skywoman/ChickenEnclosure/CAD/U Bolt.FCStd

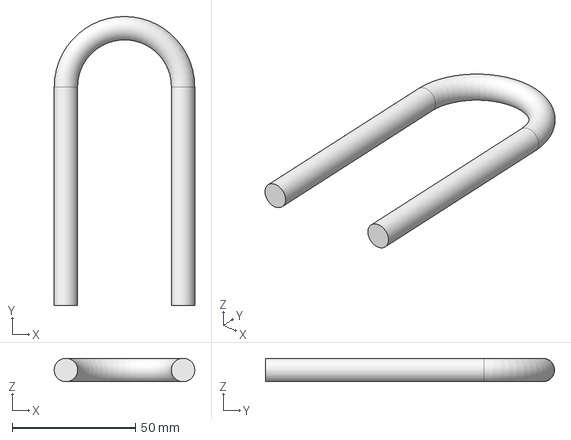
[picture p16: CAD file, 2022-02-22]
CAD/U Bolt.FCStd
57.1 x 117.5 x 9.52 mm
