skywoman/ChickenEnclosure/CAD/Hoop Connection - U Bolts/Side Bar Welded.pdf

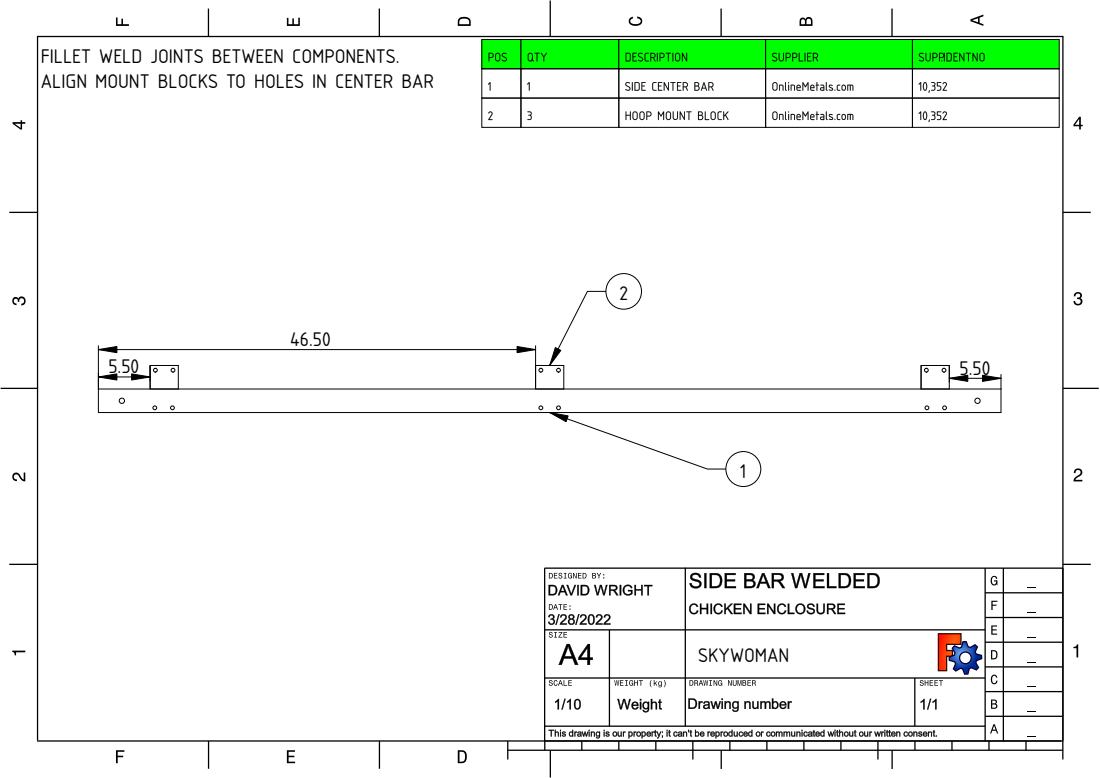
[picture p23: page 1]
SKYWOMAN

FILLET WELD JOINTS BETWEEN COMPONENTS. ALIGN MOUNT BLOCKS TO HOLES IN CENTER BAR
