skywoman/ChickenEnclosure/CAD/Hoop Connection - U Bolts/Side Front Bar.pdf

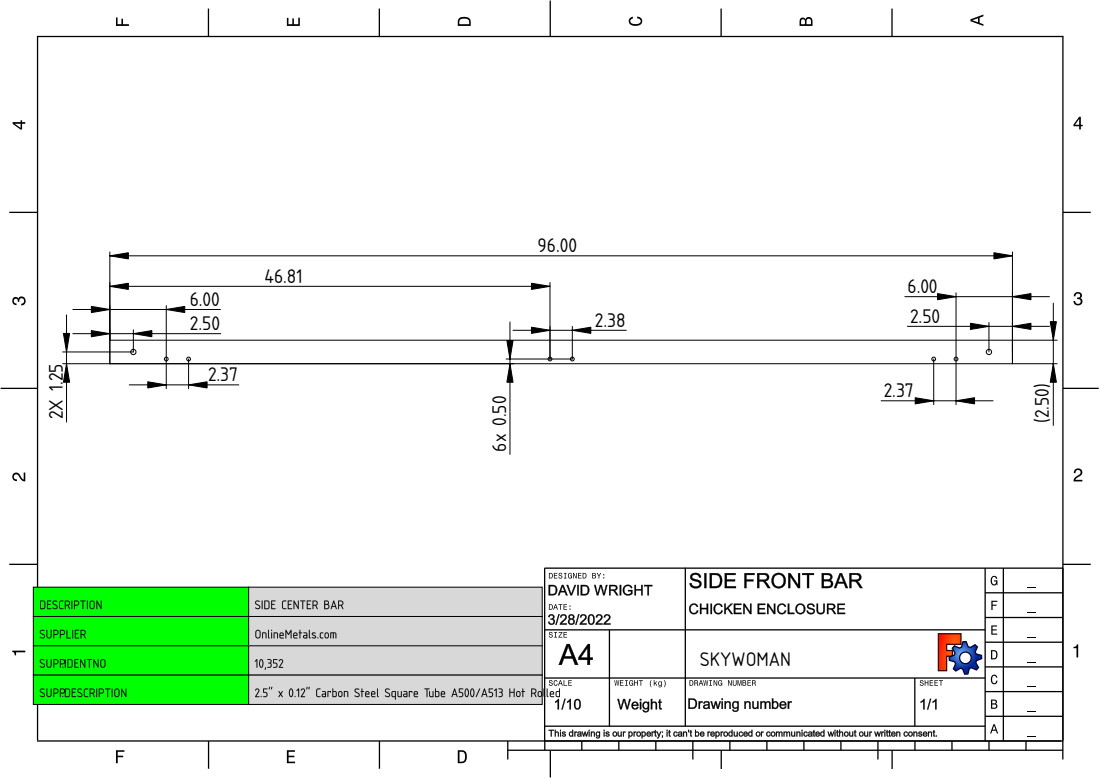
[picture p30: page 1]
