skywoman/ChickenEnclosure/CAD/Hoop Connection - U Bolts/Side Rail Joint Plate.pdf

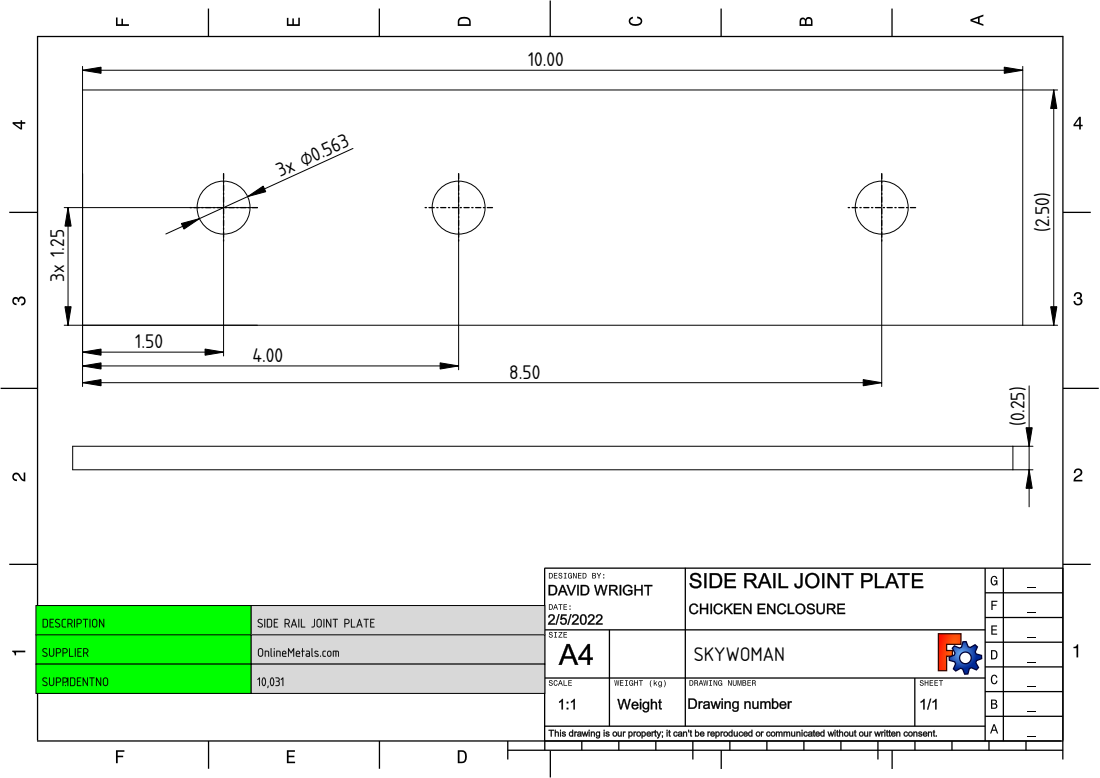
[picture p31: page 1]
