skywoman/ChickenEnclosure/CAD/Hoop Connection - U Bolts/Skid Angled Foot.pdf

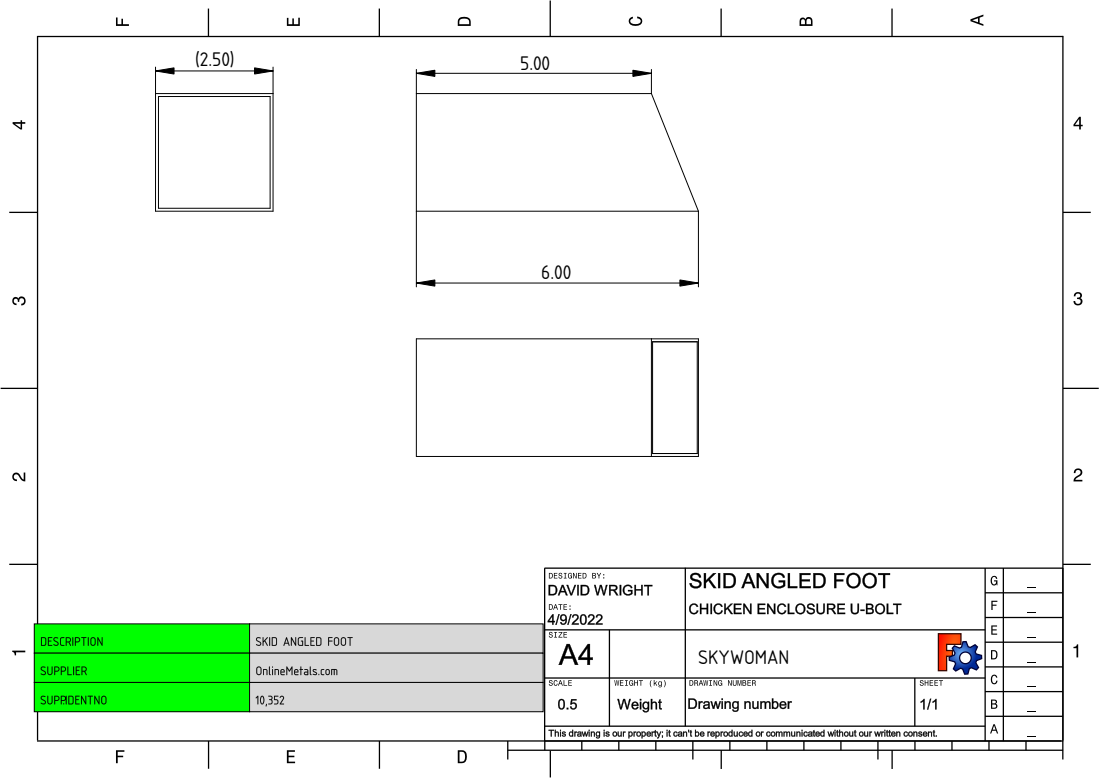
[picture p32: page 1]
SKYWOMAN
