skywoman/ChickenEnclosure/CAD/Hoop Connection - U Bolts/U Bolt.pdf

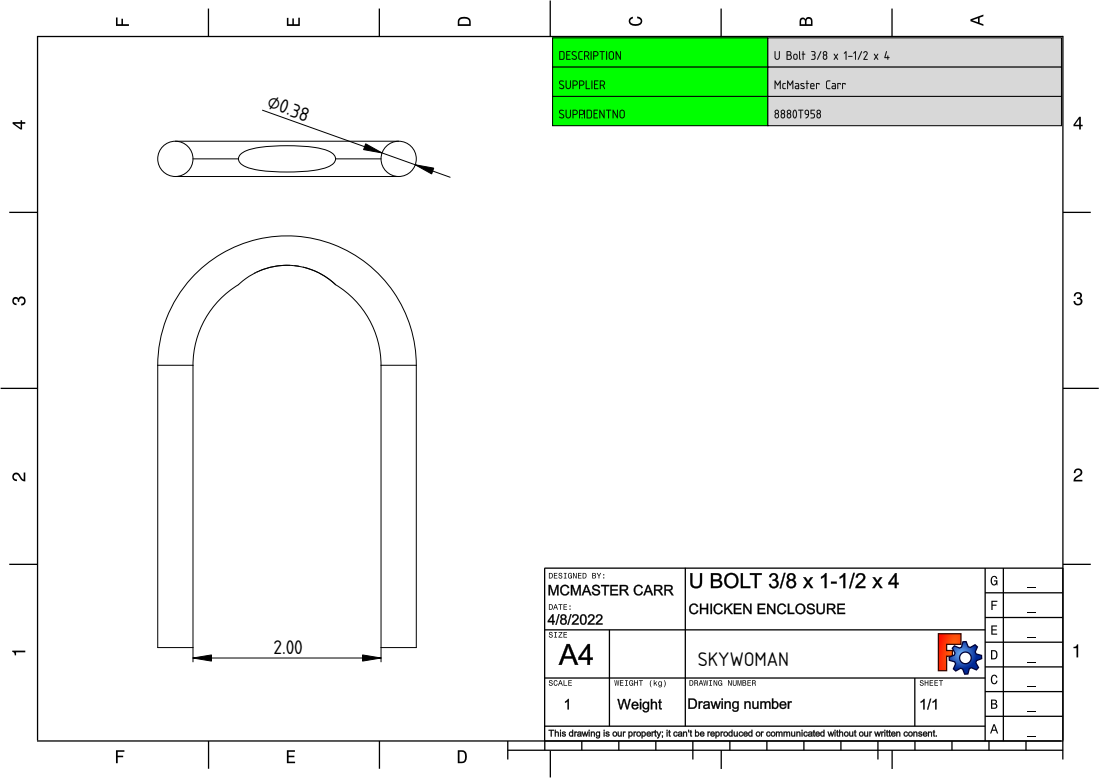
[picture p33: page 1]
SKYWOMAN
